BDS-SDCD/Soldering_Station/Station Code/Core/Src/OLED.c

#include "OLED.h"


uint8_t CharMass[]={							//Mass contains the encoding of ascii characters in the font 6x8
		0x00, 0x00, 0x00, 0x00, 0x00, 0x00,   // sp
		0x00, 0x00, 0x00, 0x2f, 0x00, 0x00,   // !
		0x00, 0x00, 0x07, 0x00, 0x07, 0x00,   // "
		0x00, 0x14, 0x7f, 0x14, 0x7f, 0x14,   // #
		0x00, 0x24, 0x2a, 0x7f, 0x2a, 0x12,   // $
		0x00, 0x23, 0x13, 0x08, 0x64, 0x62,   // %
		0x00, 0x36, 0x49, 0x55, 0x22, 0x50,   // &
		0x00, 0x00, 0x05, 0x03, 0x00, 0x00,   // '
		0x00, 0x00, 0x1c, 0x22, 0x41, 0x00,   // (
		0x00, 0x00, 0x41, 0x22, 0x1c, 0x00,   // )
		0x00, 0x14, 0x08, 0x3E, 0x08, 0x14,   // *
		0x00, 0x08, 0x08, 0x3E, 0x08, 0x08,   // +
		0x00, 0x00, 0x00, 0xA0, 0x60, 0x00,   // ,
		0x00, 0x08, 0x08, 0x08, 0x08, 0x08,   // -
		0x00, 0x00, 0x60, 0x60, 0x00, 0x00,   // .
		0x00, 0x20, 0x10, 0x08, 0x04, 0x02,   // /

		0x00, 0x3E, 0x51, 0x49, 0x45, 0x3E,   // 0
		0x00, 0x00, 0x42, 0x7F, 0x40, 0x00,   // 1
		0x00, 0x42, 0x61, 0x51, 0x49, 0x46,   // 2
		0x00, 0x21, 0x41, 0x45, 0x4B, 0x31,   // 3
		0x00, 0x18, 0x14, 0x12, 0x7F, 0x10,   // 4
		0x00, 0x27, 0x45, 0x45, 0x45, 0x39,   // 5
		0x00, 0x3C, 0x4A, 0x49, 0x49, 0x30,   // 6
		0x00, 0x01, 0x71, 0x09, 0x05, 0x03,   // 7
		0x00, 0x36, 0x49, 0x49, 0x49, 0x36,   // 8
		0x00, 0x06, 0x49, 0x49, 0x29, 0x1E,   // 9
		0x00, 0x00, 0x36, 0x36, 0x00, 0x00,   // :
		0x00, 0x00, 0x56, 0x36, 0x00, 0x00,   // ;
		0x00, 0x08, 0x14, 0x22, 0x41, 0x00,   // <
		0x00, 0x14, 0x14, 0x14, 0x14, 0x14,   // =
		0x00, 0x00, 0x41, 0x22, 0x14, 0x08,   // >
		0x00, 0x02, 0x01, 0x51, 0x09, 0x06,   // ?

		0x00, 0x32, 0x49, 0x59, 0x51, 0x3E,   // @
		0x00, 0x7C, 0x12, 0x11, 0x12, 0x7C,   // A
		0x00, 0x7F, 0x49, 0x49, 0x49, 0x36,   // B
		0x00, 0x3E, 0x41, 0x41, 0x41, 0x22,   // C
		0x00, 0x7F, 0x41, 0x41, 0x22, 0x1C,   // D
		0x00, 0x7F, 0x49, 0x49, 0x49, 0x41,   // E
		0x00, 0x7F, 0x09, 0x09, 0x09, 0x01,   // F
		0x00, 0x3E, 0x41, 0x49, 0x49, 0x7A,   // G
		0x00, 0x7F, 0x08, 0x08, 0x08, 0x7F,   // H
		0x00, 0x00, 0x41, 0x7F, 0x41, 0x00,   // I
		0x00, 0x20, 0x40, 0x41, 0x3F, 0x01,   // J
		0x00, 0x7F, 0x08, 0x14, 0x22, 0x41,   // K
		0x00, 0x7F, 0x40, 0x40, 0x40, 0x40,   // L
		0x00, 0x7F, 0x02, 0x0C, 0x02, 0x7F,   // M
		0x00, 0x7F, 0x04, 0x08, 0x10, 0x7F,   // N
		0x00, 0x3E, 0x41, 0x41, 0x41, 0x3E,   // O

		0x00, 0x7F, 0x09, 0x09, 0x09, 0x06,   // P
		0x00, 0x3E, 0x41, 0x51, 0x21, 0x5E,   // Q
		0x00, 0x7F, 0x09, 0x19, 0x29, 0x46,   // R
		0x00, 0x46, 0x49, 0x49, 0x49, 0x31,   // S
		0x00, 0x01, 0x01, 0x7F, 0x01, 0x01,   // T
		0x00, 0x3F, 0x40, 0x40, 0x40, 0x3F,   // U
		0x00, 0x1F, 0x20, 0x40, 0x20, 0x1F,   // V
		0x00, 0x3F, 0x40, 0x38, 0x40, 0x3F,   // W
		0x00, 0x63, 0x14, 0x08, 0x14, 0x63,   // X
		0x00, 0x07, 0x08, 0x70, 0x08, 0x07,   // Y
		0x00, 0x61, 0x51, 0x49, 0x45, 0x43,   // Z
		0x00, 0x00, 0x7F, 0x41, 0x41, 0x00,   // [
		0x00, 0x03, 0x0C, 0x30, 0xC0, 0x00,   // Backslash (Checker pattern)
		0x00, 0x00, 0x41, 0x41, 0x7F, 0x00,   // ]
		0x00, 0x04, 0x02, 0x01, 0x02, 0x04,   // ^
		0x00, 0x40, 0x40, 0x40, 0x40, 0x40,   // _

		0x00, 0x00, 0x03, 0x05, 0x00, 0x00,   // `
		0x00, 0x20, 0x54, 0x54, 0x54, 0x78,   // a
		0x00, 0x7F, 0x48, 0x44, 0x44, 0x38,   // b
		0x00, 0x38, 0x44, 0x44, 0x44, 0x20,   // c
		0x00, 0x38, 0x44, 0x44, 0x48, 0x7F,   // d
		0x00, 0x38, 0x54, 0x54, 0x54, 0x18,   // e
		0x00, 0x08, 0x7E, 0x09, 0x01, 0x02,   // f
		0x00, 0x18, 0xA4, 0xA4, 0xA4, 0x7C,   // g
		0x00, 0x7F, 0x08, 0x04, 0x04, 0x78,   // h
		0x00, 0x00, 0x44, 0x7D, 0x40, 0x00,   // i
		0x00, 0x40, 0x80, 0x84, 0x7D, 0x00,   // j
		0x00, 0x7F, 0x10, 0x28, 0x44, 0x00,   // k
		0x00, 0x00, 0x41, 0x7F, 0x40, 0x00,   // l
		0x00, 0x7C, 0x04, 0x18, 0x04, 0x78,   // m
		0x00, 0x7C, 0x08, 0x04, 0x04, 0x78,   // n
		0x00, 0x38, 0x44, 0x44, 0x44, 0x38,   // o

		0x00, 0xFC, 0x24, 0x24, 0x24, 0x18,   // p
		0x00, 0x18, 0x24, 0x24, 0x18, 0xFC,   // q
		0x00, 0x7C, 0x08, 0x04, 0x04, 0x08,   // r
		0x00, 0x48, 0x54, 0x54, 0x54, 0x20,   // s
		0x00, 0x04, 0x3F, 0x44, 0x40, 0x20,   // t
		0x00, 0x3C, 0x40, 0x40, 0x20, 0x7C,   // u
		0x00, 0x1C, 0x20, 0x40, 0x20, 0x1C,   // v
		0x00, 0x3C, 0x40, 0x30, 0x40, 0x3C,   // w
		0x00, 0x44, 0x28, 0x10, 0x28, 0x44,   // x
		0x00, 0x1C, 0xA0, 0xA0, 0xA0, 0x7C,   // y
		0x00, 0x44, 0x64, 0x54, 0x4C, 0x44,   // z
		0x00, 0x00, 0x10, 0x7C, 0x82, 0x00,   // {
		0x00, 0x00, 0x00, 0xFF, 0x00, 0x00,   // |
		0x00, 0x00, 0x82, 0x7C, 0x10, 0x00,   // }
		0x00, 0x00, 0x06, 0x09, 0x09, 0x06    // ~ (Degrees)
};

//----------------------------------------------------------------------------
void OLED_Send_Command(struct OLED * self,uint8_t Command){
	/**
	 * Send command to the OLED display
	 */
	uint8_t Local_Bufer[1]={0};
	Local_Bufer[0]=OLED_Command_Buffer;
	Local_Bufer[1]=Command;
	HAL_I2C_Master_Transmit(self->hi2c,self->Adress,(uint8_t *)&Local_Bufer,(uint16_t)2,1000);
}
//----------------------------------------------------------------------------
void OLED_Search_Adress(struct OLED * self){
	/**
	 *	Searching address for current OLED
	 */
	for(int i=0;i<256;i++){
			if(HAL_I2C_IsDeviceReady((self->hi2c),i,10,2)==HAL_OK){
				self->Adress=i;
				break;
			}
		}
}
//----------------------------------------------------------------------------

void OLED_ini(struct OLED * self){
	/**
	 * Command initialization of OLED display
	 */
	OLED_Send_Command(self,0xAF);		//Display on/off

	OLED_Send_Command(self,0xA6);		//Normal/inverse color mode

	OLED_Send_Command(self,0x20);		//Set page address mode
	OLED_Send_Command(self,0x0);

	OLED_Send_Command(self,0x8d);		//Pump Charge

	OLED_Send_Command(self,0xA4);		//Entire display on (output flows/ignore ram)

	OLED_Send_Command(self,0xA0);		//Segment re-map

	OLED_Send_Command(self,0xC7);		//Com output right direction/inverse direction

	OLED_Clear_Display(self);

	OLED_Send_Command(self,0x21);    	//Set COM remap value(Set Column Address)
	OLED_Send_Command(self,0x1);			//1
	OLED_Send_Command(self,0x7E);		//126

	OLED_Send_Command(self,0x22);		//Set Page Address
	OLED_Send_Command(self,0x0);
	OLED_Send_Command(self,0x7);

}
//----------------------------------------------------------------------------
void OLED_Set_Cursor(struct OLED * self,uint16_t x,uint8_t y){
	/**
	 * Sets position on display from what will be display
	 */
	OLED_Send_Command(self,0xB0|y);
	OLED_Send_Command(self,x & 0x0F);
	OLED_Send_Command(self,((x>>4) & 0x0F)+0x10);
}
//----------------------------------------------------------------------------
void OLED_Set_Char_Cursor(struct OLED * self, uint16_t x,uint8_t y){
	/**
	 * Sets position on display from what will be display based on ASII symbols size
	 */
	x*=6;
	OLED_Send_Command(self,0xB0|y);
	OLED_Send_Command(self,x & 0x0F);
	OLED_Send_Command(self,((x>>4) & 0x0F)+0x10);
}
//----------------------------------------------------------------------------
void OLED_Clear_Display(struct OLED * self){
	/**
	 * Clear OLED display
	 */
	uint8_t Local_Bufer[129]={0};
	Local_Bufer[0]=OLED_Data_Buffer;
	for(uint8_t j=0;j<8;j++){
		OLED_Set_Cursor(self,0,j);
		HAL_I2C_Master_Transmit(self->hi2c,self->Adress,(uint8_t *)&Local_Bufer,(uint16_t)129,1000);
		}
}
//----------------------------------------------------------------------------
void OLED_Send_Char(struct OLED * self, uint8_t data){
	/**
	 * Drawing char on a OLED display
	 */
	uint8_t Local_Bufer[7]={0};
	Local_Bufer[0]=OLED_Data_Buffer;
	int sp=(data-(int)' ')*6;
	for(int j=1;j<7;j++)
		Local_Bufer[j]=CharMass[sp+j-1];

	HAL_I2C_Master_Transmit(self->hi2c,self->Adress,(uint8_t *)&Local_Bufer,(uint16_t)7,1000);

}
//----------------------------------------------------------------------------
void OLED_Clear_Char(struct OLED * self,uint16_t x, uint8_t y){
	/**
	 * Clear char on a OLED display
	 */
	OLED_Set_Char_Cursor(self,x, y);
	OLED_Send_Char(self,' ');
}
//----------------------------------------------------------------------------
void OLED_Clear_Line (struct OLED * self, uint8_t y){
	/**
	 * Clear line on OLED display
	 */
	uint8_t Local_Bufer[127]={0};
	Local_Bufer[0]=OLED_Data_Buffer;
	OLED_Set_Cursor(self,0,y);
	HAL_I2C_Master_Transmit(self->hi2c,self->Adress,(uint8_t *)&Local_Bufer,(uint16_t)127,1000);
}
//----------------------------------------------------------------------------
void OLED_Send_String(struct OLED * self,char* str, enum Display_Write_MODE Display_Write_MODE){
	/**
	 * Drawing string on a OLED display
	 */
	uint8_t *Local_Buffer=malloc(sizeof(uint8_t)*strlen(str)*6+1);	//Create a local buffer for str*6(because every symbol has size 6) +1 for data address
	Local_Buffer[0]=OLED_Data_Buffer;							//Set buffer address as first transfered data

	int i=0,													//i sift string symbol every iteration
		sp;														//Contain the first column of symbol
	uint8_t j;
	uint16_t counter=0;											//Count quantity of symbols
	while(str[i]!='\0'){										//Loop while str not end
		if(str[i]=='\r'||str[i]=='\n'){							//filter all another special symbols
			i++;
			continue;
		}
		sp=(str[i]-(int)' ')*6;									//Computing the first column of symbol
		for(j=0;j<6;j++){										//Write 6 column of symbol based on Display_Write_MODE
			if(Display_Write_MODE==Direct_Display_MODE)
				Local_Buffer[(j+counter*6)+1]=CharMass[sp+j];
			else
				Local_Buffer[(j+counter*6)+1]=~CharMass[sp+j];
		}
		i++;
		counter++;
	}
	HAL_I2C_Master_Transmit(self->hi2c,self->Adress,Local_Buffer,(uint16_t)(counter*6)+1,1000);
	free(Local_Buffer);
}
//----------------------------------------------------------------------------
